liveboxandy/ZX-Max-128-Issue-3A/Step/DIP-16_W7.62mm_Socket.step

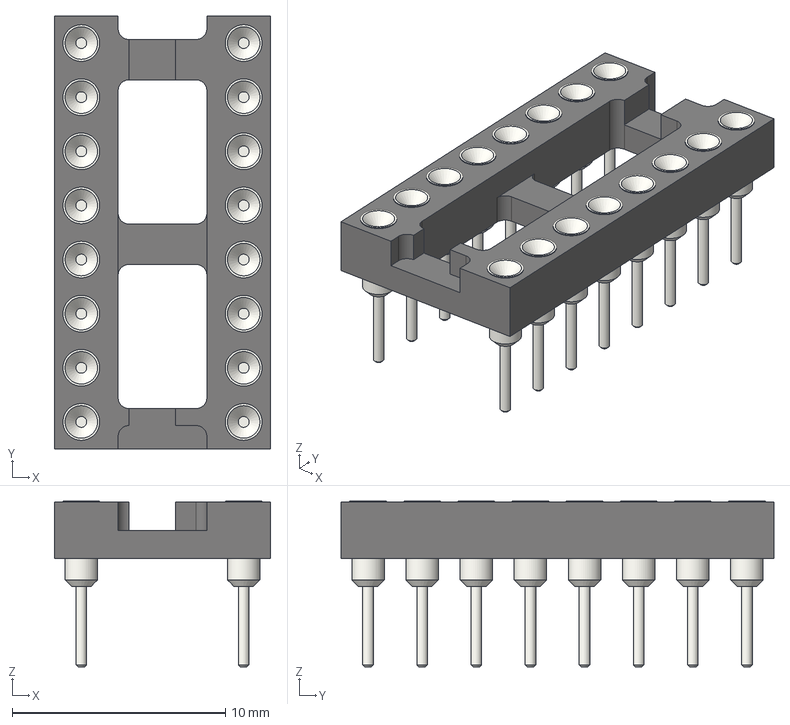
[picture p17: CAD file, 2026-07-10]
Step/DIP-16_W7.62mm_Socket.step
10.2 x 20.3 x 7.79 mm
