liveboxandy/ZX-Max-128-Issue-3A/Step/DIP-40_W15.24mm_Socket.step

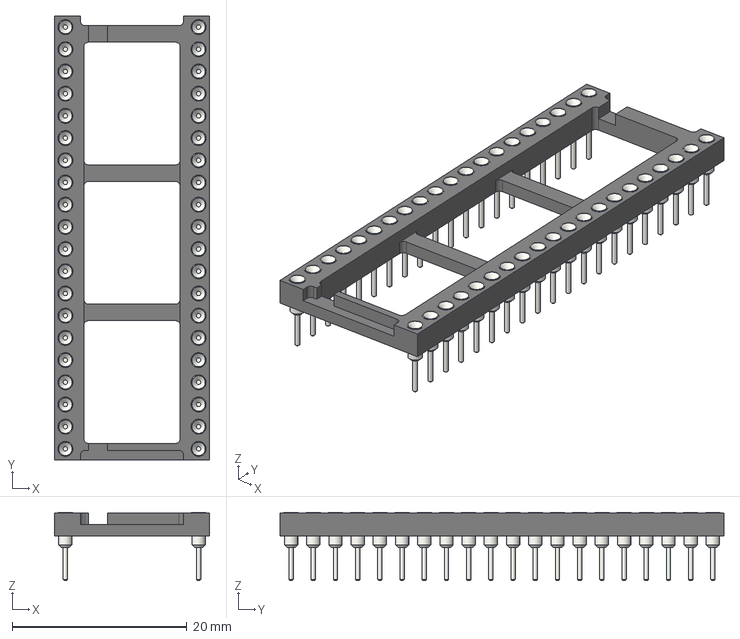
[picture p20: CAD file, 2026-07-10]
Step/DIP-40_W15.24mm_Socket.step
17.8 x 50.8 x 7.79 mm
