liveboxandy/ZX-Max-128-Issue-3A/Step/Voltage Regulator AZ1117IH-3.3TRG1.step

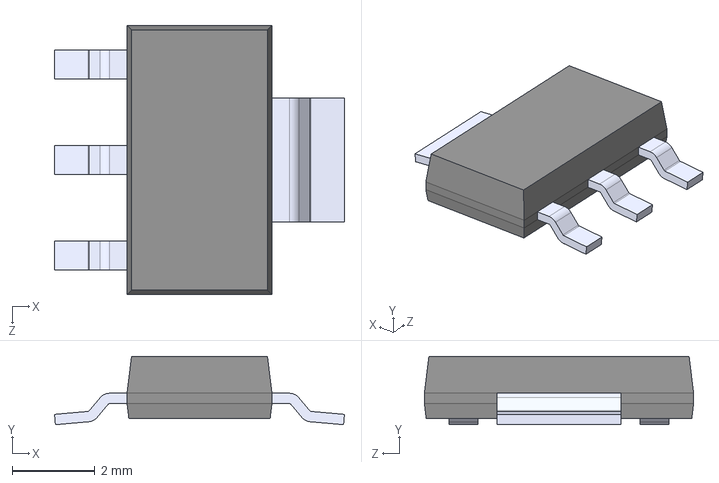
[picture p22: CAD file, 2026-07-10]
Step/Voltage Regulator AZ1117IH-3.3TRG1.step
7.00 x 1.65 x 6.50 mm
