liveboxandy/ZX-Max-128-Issue-3A/Step/PJ-002A.step

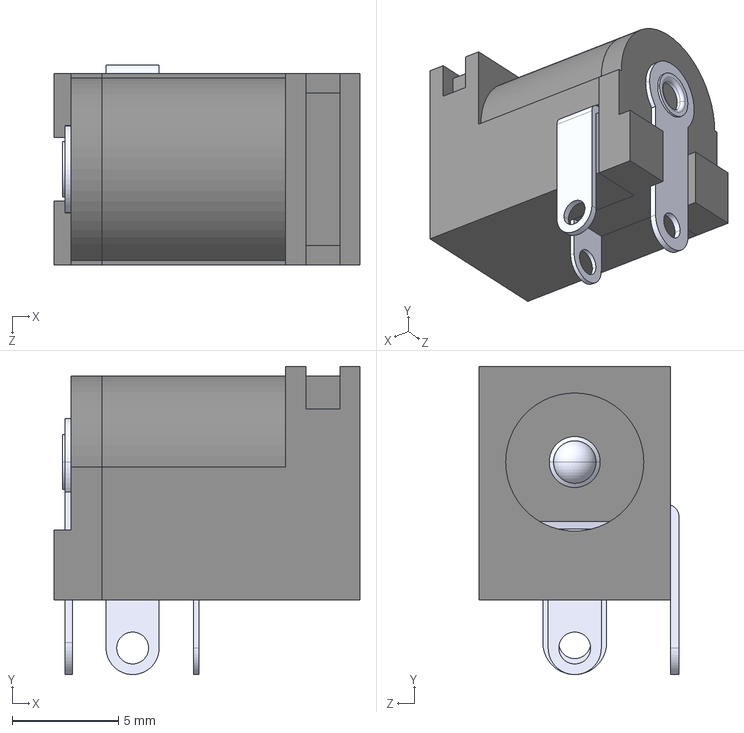
[picture p23: CAD file, 2026-07-10]
Step/PJ-002A.step
14.4 x 14.5 x 9.40 mm
