liveboxandy/ZX-Max-128-Issue-3A/Step/PLCC-84-AT.stp

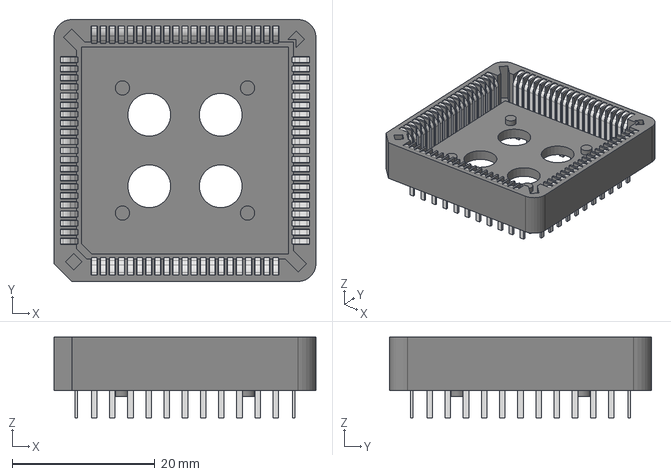
[picture p25: CAD file, 2026-07-10]
Step/PLCC-84-AT.stp
36.7 x 36.7 x 11.3 mm
