liveboxandy/ZX-Max-128-Issue-3A/Step/Capacitor 10nF 100V MLCC FA18C0G2A103JRU06.step

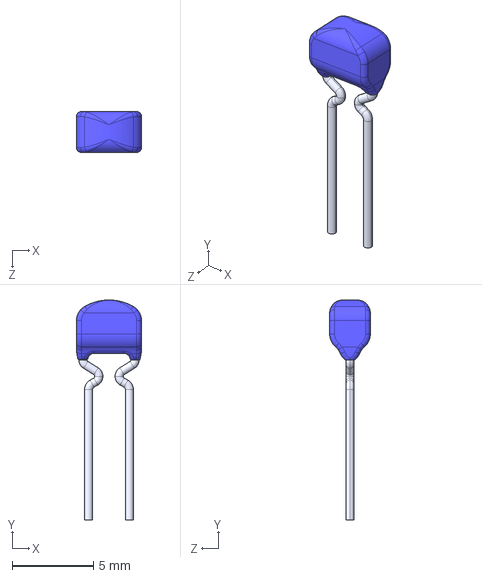
[picture p26: CAD file, 2026-07-10]
Step/Capacitor 10nF 100V MLCC FA18C0G2A103JRU06.step
4.00 x 13.5 x 2.50 mm
