liveboxandy/ZX-Max-128-Issue-3A/Step/DIP-16_W7.62mm.step

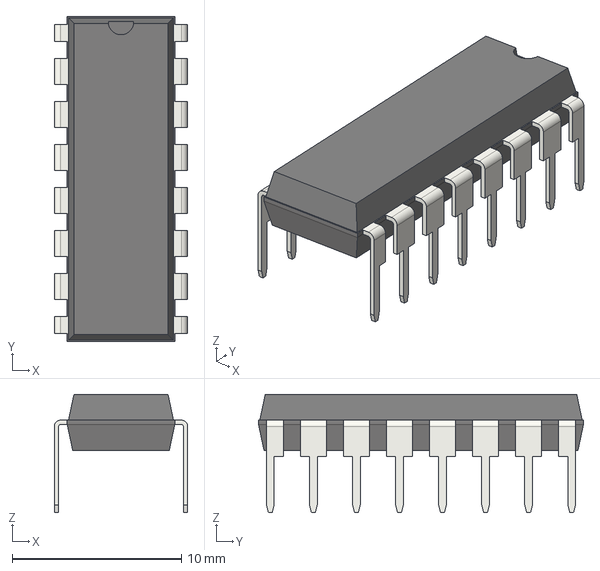
[picture p28: CAD file, 2026-07-10]
Step/DIP-16_W7.62mm.step
7.87 x 19.2 x 6.98 mm
