liveboxandy/ZX-Max-128-Issue-3A/Step/DIP-28_W15.24mm.step

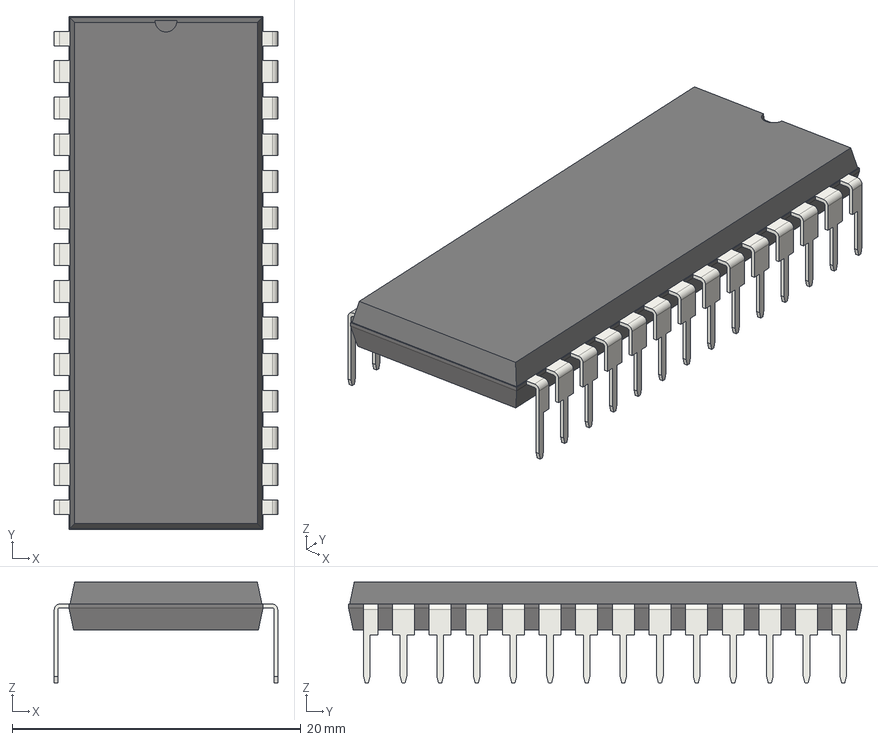
[picture p29: CAD file, 2026-07-10]
Step/DIP-28_W15.24mm.step
15.5 x 35.6 x 6.98 mm
