liveboxandy/ZX-Max-128-Issue-3A/Step/DIP-14_W7.62mm.step

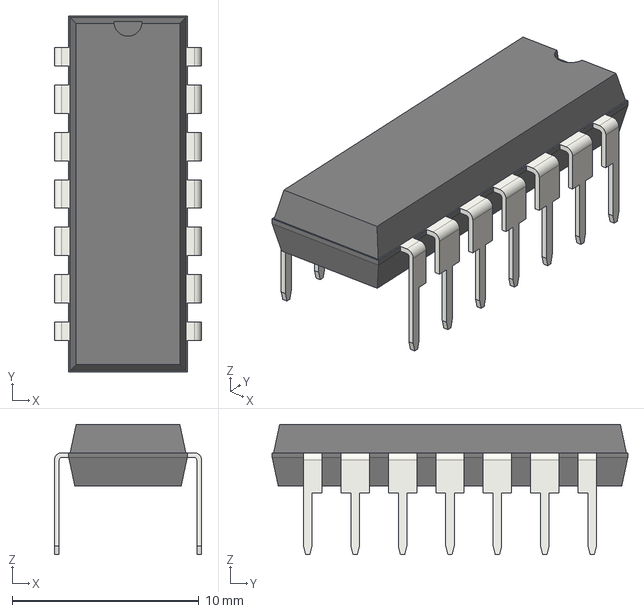
[picture p30: CAD file, 2026-07-10]
Step/DIP-14_W7.62mm.step
7.87 x 19.1 x 6.98 mm
