liveboxandy/ZX-Max-128-Issue-3A/Step/9Pin MiniDIN KMDGX-9S-BS-1_A1.IGS

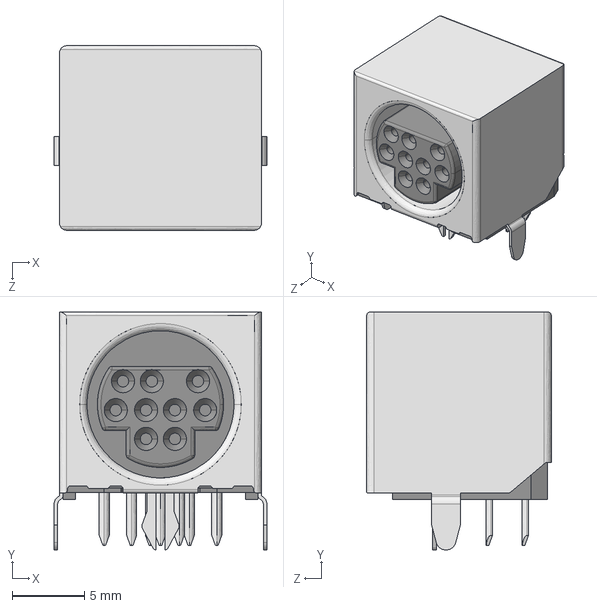
[picture p33: CAD file, 2026-07-10]
Step/9Pin MiniDIN KMDGX-9S-BS-1_A1.IGS
14.8 x 16.5 x 12.8 mm
