liveboxandy/ZX-Max-128-Issue-3A/Step/DIP-32_W15.24mm.step

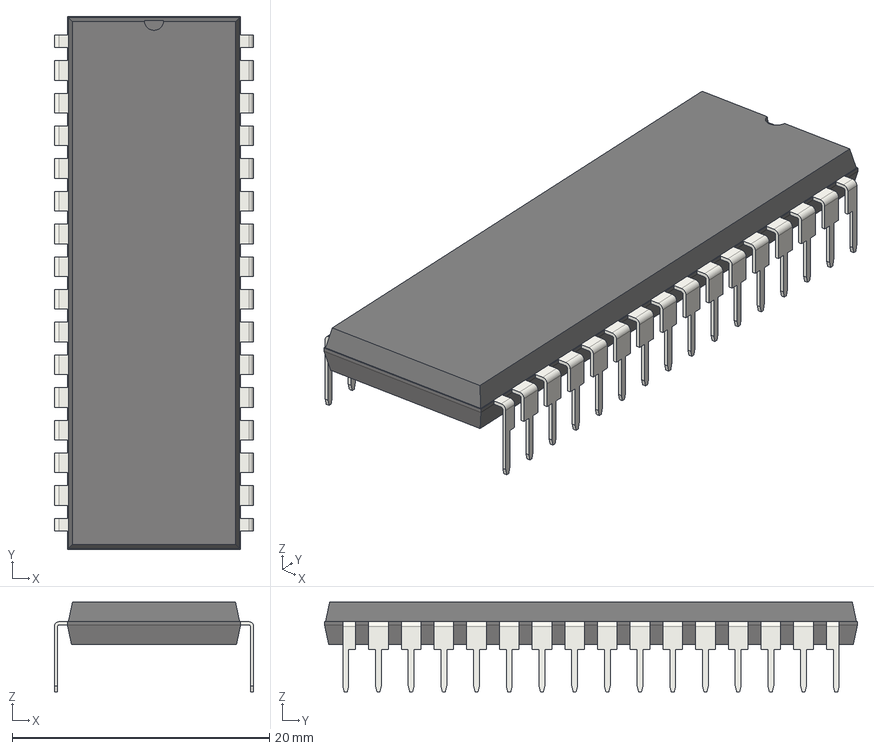
[picture p34: CAD file, 2026-07-10]
Step/DIP-32_W15.24mm.step
15.5 x 41.4 x 6.98 mm
