liveboxandy/ZX-Max-128-Issue-3A/Step/Capacitor 10uF 25V ECA-1EM100B.stp

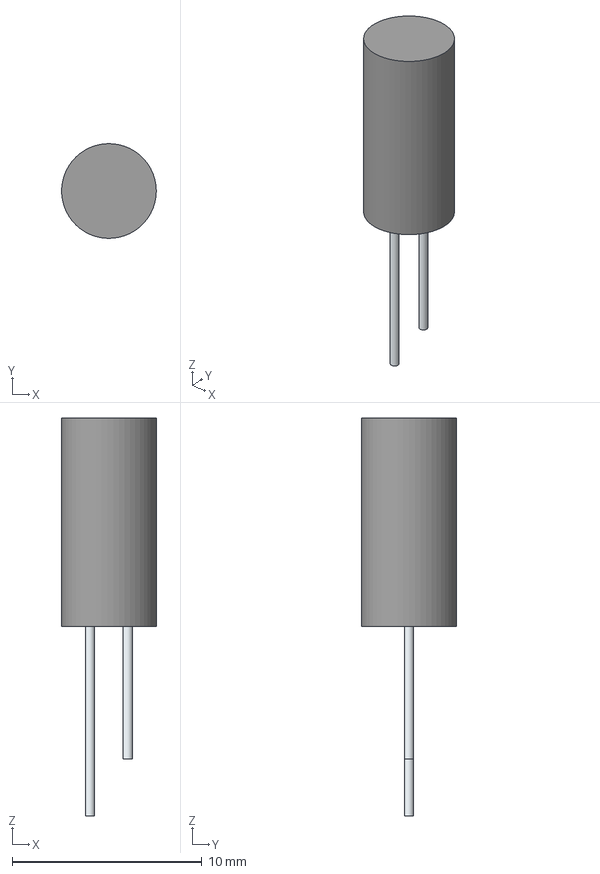
[picture p35: CAD file, 2026-07-10]
Step/Capacitor 10uF 25V ECA-1EM100B.stp
5.00 x 5.00 x 21.0 mm
SimpleBody
Pin1
Pin2
