liveboxandy/ZX-Max-128-Issue-3A/Step/Connector Pin-Pin 1x2 M20-9990246.step

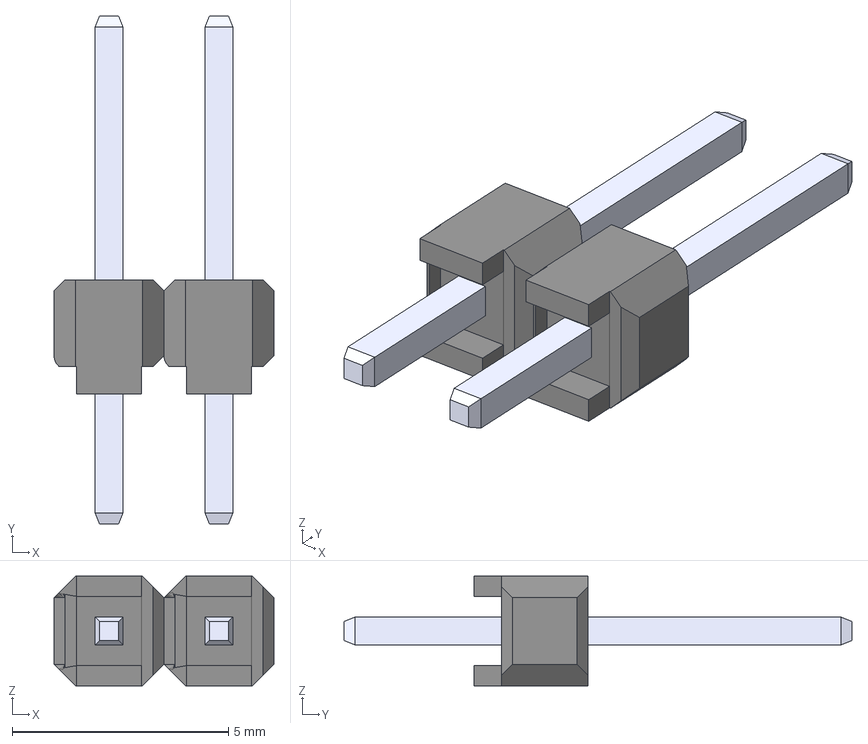
[picture p36: CAD file, 2026-07-10]
Step/Connector Pin-Pin 1x2 M20-9990246.step
5.08 x 11.7 x 2.54 mm
