liveboxandy/ZX-Max-128-Issue-3A/Step/9Pin MiniDIN KMDGX-9S-BS-1.stp

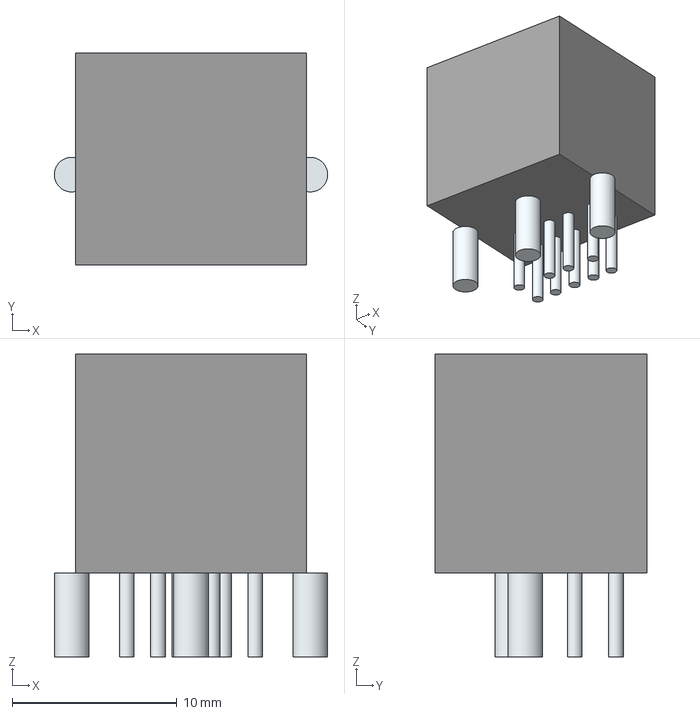
[picture p37: CAD file, 2026-07-10]
Step/9Pin MiniDIN KMDGX-9S-BS-1.stp
16.6 x 12.9 x 18.4 mm
Leads
