liveboxandy/ZX-Max-128-Issue-3A/Step/AS6C6264-55PCN.stp

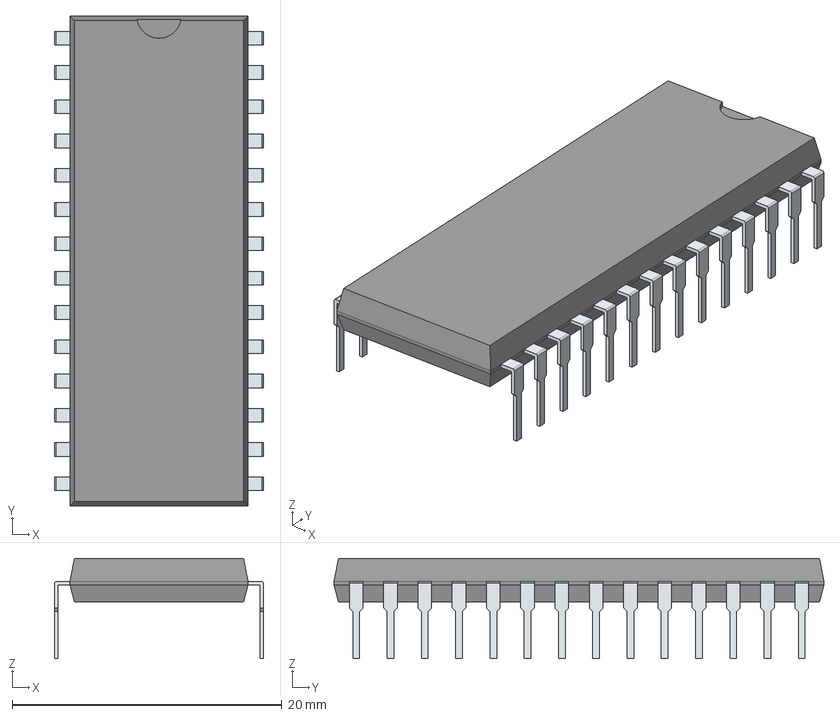
[picture p38: CAD file, 2026-07-10]
Step/AS6C6264-55PCN.stp
15.5 x 36.3 x 7.44 mm
PinsArrayLR
