liveboxandy/ZX-Max-128-Issue-3A/Step/AT27C256R-45PU.stp

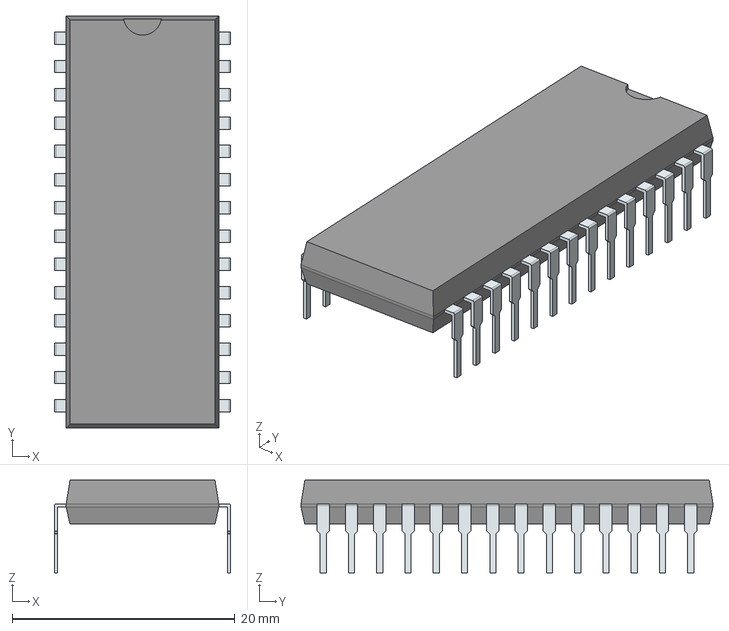
[picture p41: CAD file, 2026-07-10]
Step/AT27C256R-45PU.stp
15.8 x 37.0 x 8.33 mm
PinsArrayLR
