liveboxandy/ZX-Max-128-Issue-3A/CPU-ROM-RAM.kicad_sch

## KiCad design CPU-ROM-RAM.kicad_sch (2026-07-10)

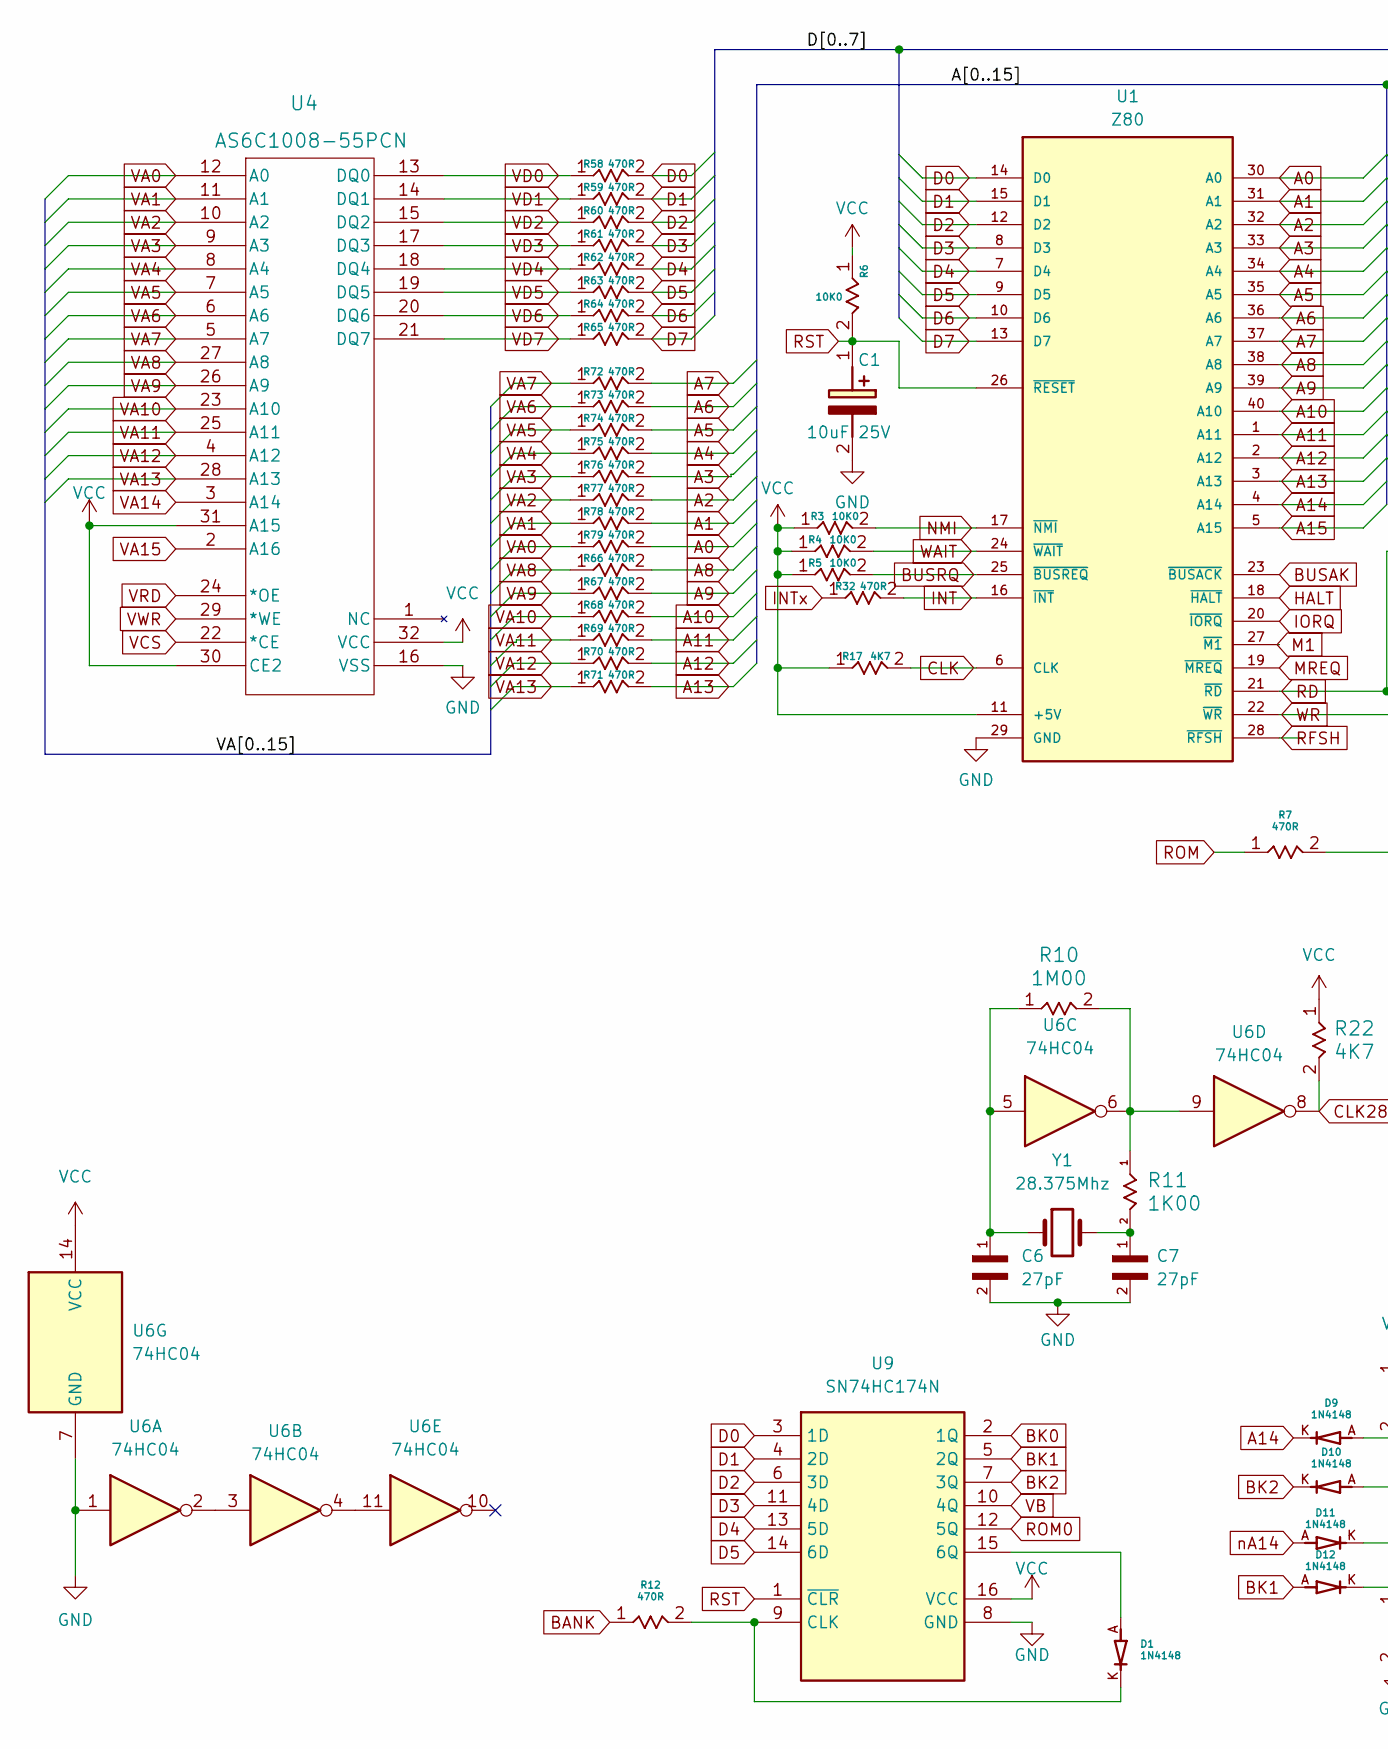
[picture p48: schematic CPU-ROM-RAM.kicad_sch, part in row 1, column 1]

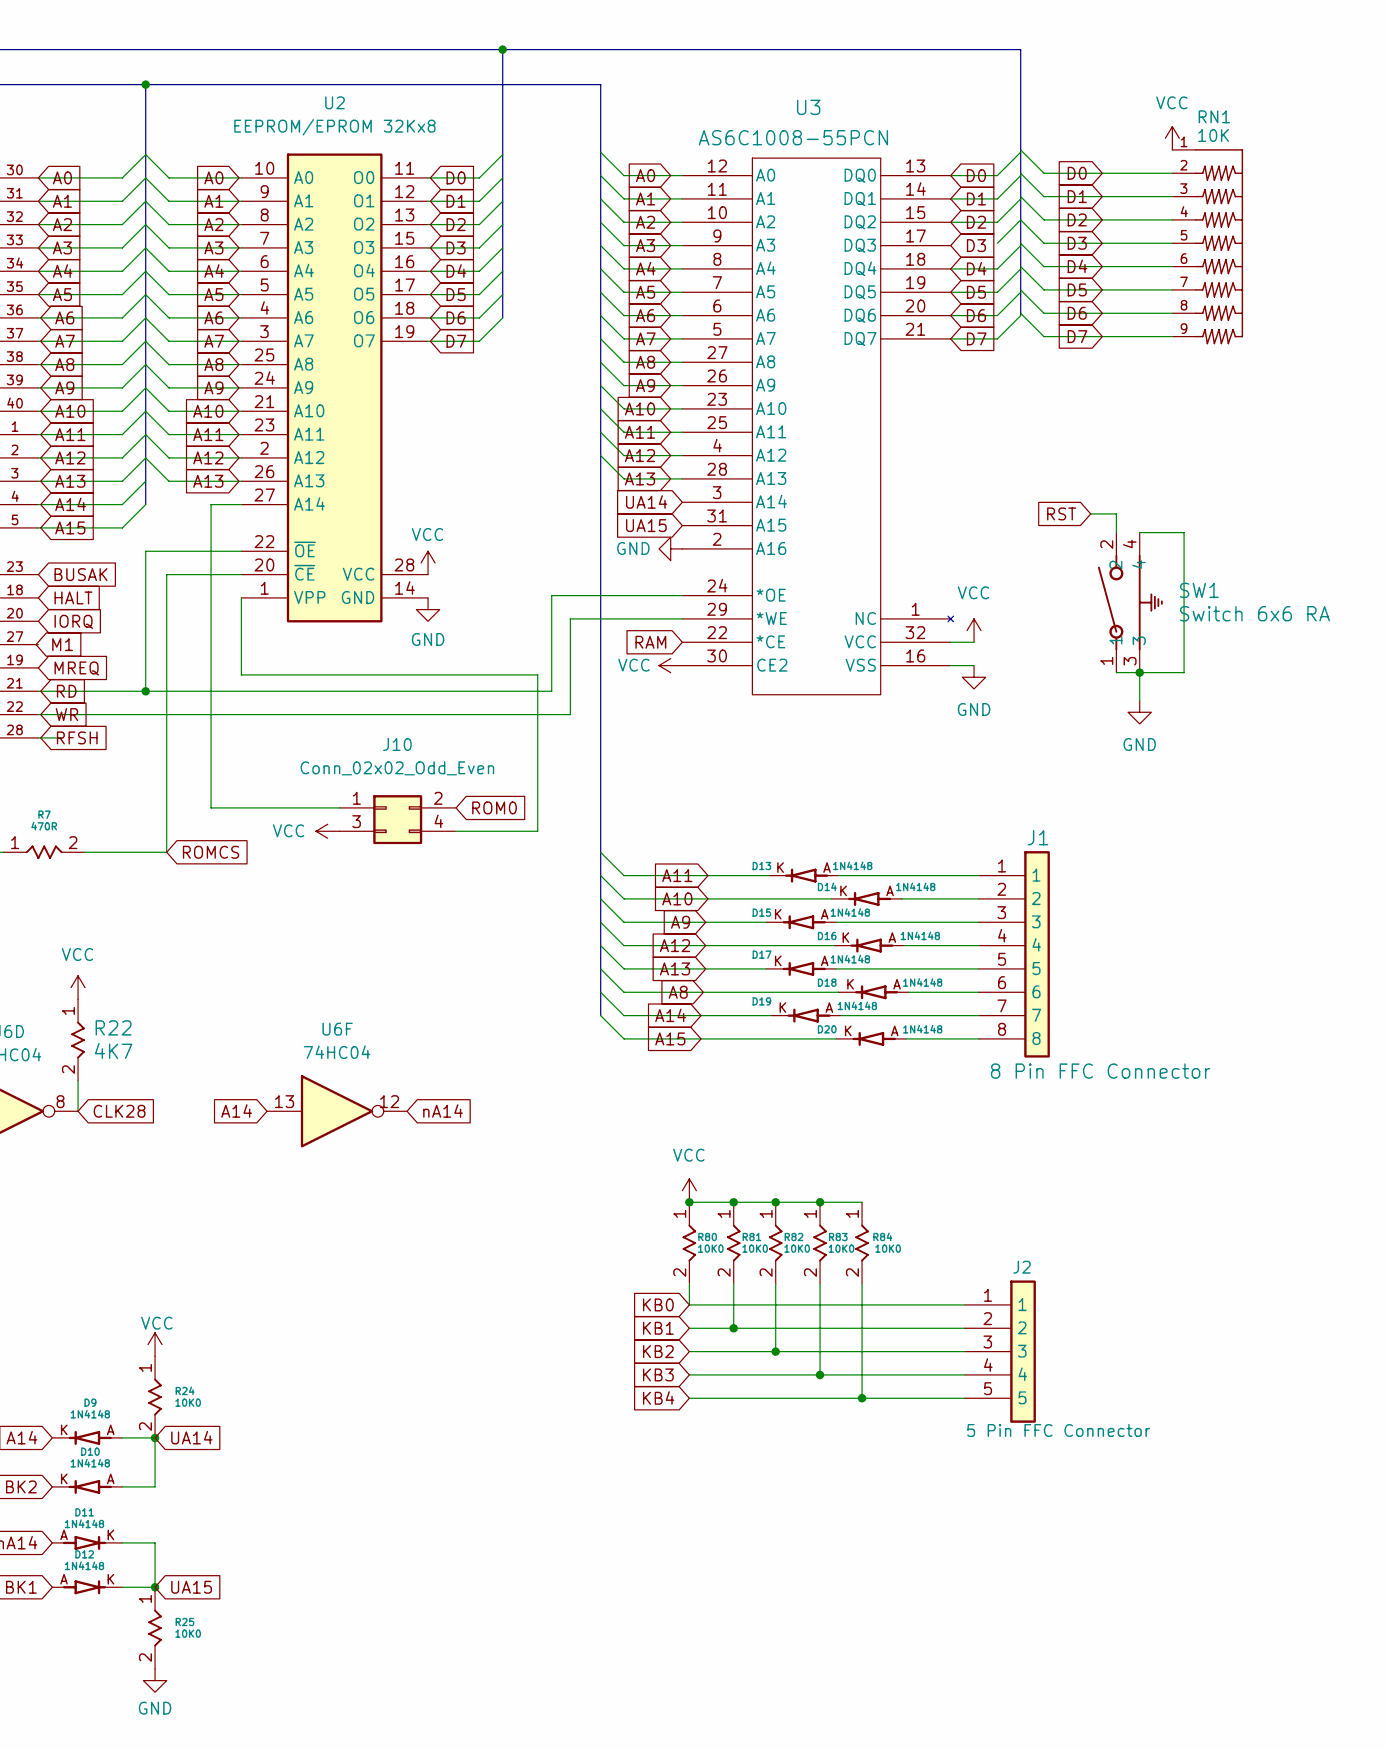
[picture p49: schematic CPU-ROM-RAM.kicad_sch, part in row 1, column 2]

Parts:
C1: 10uF 25V; CAPPRD200W50D500H1100; Mouser Part Number 667-ECA-1EM100B
C6, C7: 27pF; CAPRB250W50L400T250H550; PARTREV 20200310
D1, D9, D10, D11, D12, D13, D14, D15, D16, D17, D18, D19, D20: 1N4148; DIOAD753W49L380D172B; PARTREV 5
J1: 8 Pin FFC Connector; 55203155
J2: 5 Pin FFC Connector; 55203155; Mouser Part Number 571-5-520315-5
J10: Conn_02x02_Odd_Even; PinHeader_2x02_P2.54mm_Vertical
R3, R4, R5, R6, R24, R25, R80, R81, R82, R83, R84: 10K0; STA_CF14_STP
R7, R12, R32, R58, R59, R60, R61, R62, R63, R64, R65, R66, R67, R68, R69, R70, R71, R72, R73, R74, R75, R76, R77, R78, R79: 470R; STA_CF14_STP
R10: 1M00; STA_CF14_STP
R11: 1K00; STA_CF14_STP
R17, R22: 4K7; STA_CF14_STP
RN1: 10K; SIP249W50P254L2281H508Q9; PARTREV 10/1/20
SW1: Switch 6x6 RA; SW2_1825027-G_TEC
U1: Z80; Z80_Socket
U2: EEPROM/EPROM 32Kx8; DIP1556W56P254L3702H483Q28N; Mouser Part Number 556-AT27C256R-45PU
U3: AS6C1008-55PCN; U3
U4: AS6C1008-55PCN; PDIP-32_MIL600_ALL
U6: 74HC04; DIP794W53P254L1930H508Q14N
U9: SN74HC174N; DIP794W53P254L1930H508Q16N; Mouser Part Number 595-SN74HC174N
Y1: 28.375Mhz; Crystal_HC49-4H_Vertical

Connections:
A0: R79.2, U1.30 (A0), U2.10 (A0), U3.12 (A0)
A1: R78.2, U1.31 (A1), U2.9 (A1), U3.11 (A1)
A2: R77.2, U1.32 (A2), U2.8 (A2), U3.10 (A2)
A3: R76.2, U1.33 (A3), U2.7 (A3), U3.9 (A3)
A4: R75.2, U1.34 (A4), U2.6 (A4), U3.8 (A4)
A5: R74.2, U1.35 (A5), U2.5 (A5), U3.7 (A5)
A6: R73.2, U1.36 (A6), U2.4 (A6), U3.6 (A6)
A7: R72.2, U1.37 (A7), U2.3 (A7), U3.5 (A7)
A8: D18.K, R66.2, U1.38 (A8), U2.25 (A8), U3.27 (A8)
A9: D15.K, R67.2, U1.39 (A9), U2.24 (A9), U3.26 (A9)
A10: D14.K, R68.2, U1.40 (A10), U2.21 (A10), U3.23 (A10)
A11: D13.K, R69.2, U1.1 (A11), U2.23 (A11), U3.25 (A11)
A12: D16.K, R70.2, U1.2 (A12), U2.2 (A12), U3.4 (A12)
A13: D17.K, R71.2, U1.3 (A13), U2.26 (A13), U3.28 (A13)
A14: D9.K, D19.K, U1.4 (A14), U6.13
A15: D20.K, U1.5 (A15)
BANK: R12.1
BK0: U9.2 (1Q)
BK1: D12.A, U9.5 (2Q)
BK2: D10.K, U9.7 (3Q)
BUSAK: U1.23 (~BUSACK)
BUSRQ: R5.2, U1.25 (~BUSREQ)
CLK: R17.2, U1.6 (CLK)
CLK28: R22.2, U6.8
D0: R58.2, RN1.2, U1.14 (D0), U2.11 (O0), U3.13 (DQ0), U9.3 (1D)
D1: R59.2, RN1.3, U1.15 (D1), U2.12 (O1), U3.14 (DQ1), U9.4 (2D)
D2: R60.2, RN1.4, U1.12 (D2), U2.13 (O2), U3.15 (DQ2), U9.6 (3D)
D3: R61.2, RN1.5, U1.8 (D3), U2.15 (O3), U3.17 (DQ3), U9.11 (4D)
D4: R62.2, RN1.6, U1.7 (D4), U2.16 (O4), U3.18 (DQ4), U9.13 (5D)
D5: R63.2, RN1.7, U1.9 (D5), U2.17 (O5), U3.19 (DQ5), U9.14 (6D)
D6: R64.2, RN1.8, U1.10 (D6), U2.18 (O6), U3.20 (DQ6)
D7: R65.2, RN1.9, U1.13 (D7), U2.19 (O7), U3.21 (DQ7)
GND: C1.2 (-), C6.2, C7.2, R25.2, SW1.1, SW1.3, SW1.4, U1.29 (GND), U2.14 (GND), U3.2 (A16), U3.16 (VSS), U4.16 (VSS), U6.1, U6.7 (GND), U9.8 (GND)
HALT: U1.18 (~HALT)
INT: R32.2, U1.16 (~INT)
INTx: R32.1
IORQ: U1.20 (~IORQ)
KB0: J2.1, R80.2
KB1: J2.2, R81.2
KB2: J2.3, R82.2
KB3: J2.4, R83.2
KB4: J2.5, R84.2
M1: U1.27 (~M1)
MREQ: U1.19 (~MREQ)
NMI: R3.2, U1.17 (~NMI)
unnamed: C6.1, R10.1, U6.5, Y1.1
unnamed: C7.1, R11.2, Y1.2
unnamed: D1.A, U9.15 (6Q)
unnamed: D1.K, R12.2, U9.9 (CLK)
unnamed: D13.A, J1.1
unnamed: D14.A, J1.2
unnamed: D15.A, J1.3
unnamed: D16.A, J1.4
unnamed: D17.A, J1.5
unnamed: D18.A, J1.6
unnamed: D19.A, J1.7
unnamed: D20.A, J1.8
unnamed: J10.1, U2.27 (A14)
unnamed: J10.4, U2.1 (VPP)
unnamed: R10.2, R11.1, U6.6, U6.9
unnamed: U6.2, U6.3
unnamed: U6.4, U6.11
RAM: U3.22 (*CE)
RD: U1.21 (~RD), U2.22 (~OE), U3.24 (*OE)
RFSH: U1.28 (~RFSH)
ROM: R7.1
ROM0: J10.2, U9.12 (5Q)
ROMCS: R7.2, U2.20 (~CE)
RST: C1.1 (+), R6.2, SW1.2, U1.26 (~RESET), U9.1 (~CLR)
UA14: D9.A, D10.A, R24.2, U3.3 (A14)
UA15: D11.K, D12.K, R25.1, U3.31 (A15)
VA0: R79.1, U4.12 (A0)
VA1: R78.1, U4.11 (A1)
VA2: R77.1, U4.10 (A2)
VA3: R76.1, U4.9 (A3)
VA4: R75.1, U4.8 (A4)
VA5: R74.1, U4.7 (A5)
VA6: R73.1, U4.6 (A6)
VA7: R72.1, U4.5 (A7)
VA8: R66.1, U4.27 (A8)
VA9: R67.1, U4.26 (A9)
VA10: R68.1, U4.23 (A10)
VA11: R69.1, U4.25 (A11)
VA12: R70.1, U4.4 (A12)
VA13: R71.1, U4.28 (A13)
VA14: U4.3 (A14)
VA15: U4.2 (A16)
VB: U9.10 (4Q)
VCC: J10.3, R3.1, R4.1, R5.1, R6.1, R17.1, R22.1, R24.1, R80.1, R81.1, R82.1, R83.1, R84.1, RN1.1, U1.11 (+5V), U2.28 (VCC), U3.30 (CE2), U3.32 (VCC), U4.30 (CE2), U4.31 (A15), U4.32 (VCC), U6.14 (VCC), U9.16 (VCC)
VCS: U4.22 (*CE)
VD0: R58.1, U4.13 (DQ0)
VD1: R59.1, U4.14 (DQ1)
VD2: R60.1, U4.15 (DQ2)
VD3: R61.1, U4.17 (DQ3)
VD4: R62.1, U4.18 (DQ4)
VD5: R63.1, U4.19 (DQ5)
VD6: R64.1, U4.20 (DQ6)
VD7: R65.1, U4.21 (DQ7)
VRD: U4.24 (*OE)
VWR: U4.29 (*WE)
WAIT: R4.2, U1.24 (~WAIT)
WR: U1.22 (~WR), U3.29 (*WE)
nA14: D11.A, U6.12
