liveboxandy/ZX-Max-128-Issue-3A/EPM7128S.kicad_sch

## KiCad design EPM7128S.kicad_sch (2026-07-10)

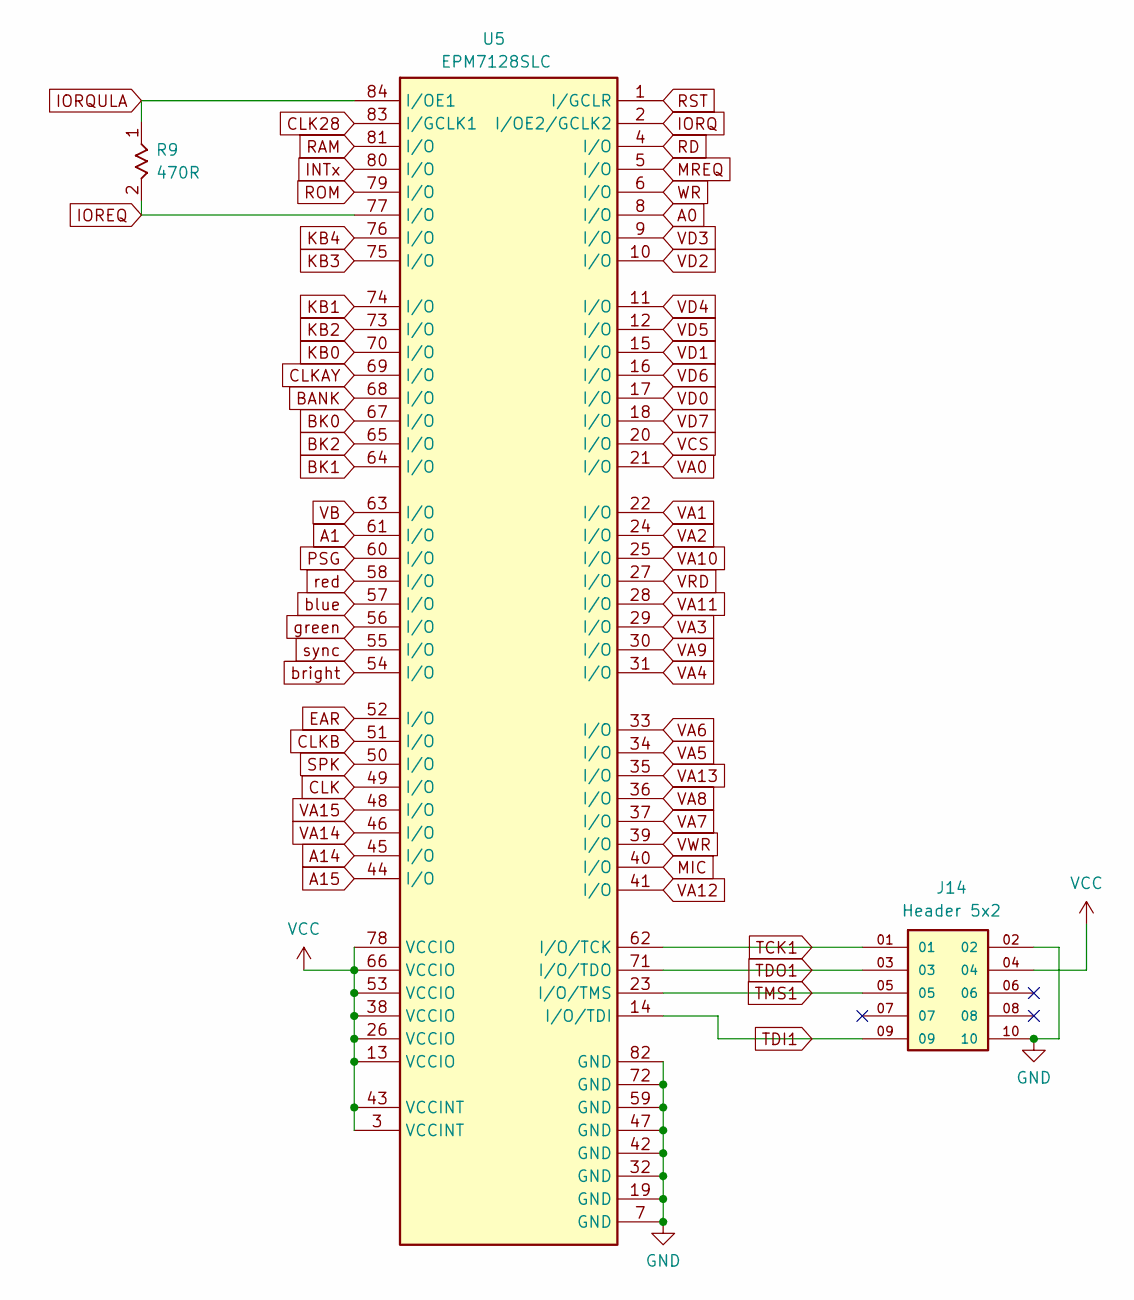
[picture p50: schematic EPM7128S.kicad_sch]

Parts:
J14: Header 5x2; AMPHENOL_10129381-910002BLF; PARTREV D
R9: 470R; STA_CF14_STP
U5: EPM7128SLC; PLCC84AT

Connections:
A0: U5.8 (I/O)
A1: U5.61 (I/O)
A14: U5.45 (I/O)
A15: U5.44 (I/O)
BANK: U5.68 (I/O)
BK0: U5.67 (I/O)
BK1: U5.64 (I/O)
BK2: U5.65 (I/O)
CLK: U5.49 (I/O)
CLK28: U5.83 (I/GCLK1)
CLKAY: U5.69 (I/O)
CLKB: U5.51 (I/O)
EAR: U5.52 (I/O)
GND: J14.02, J14.10, U5.7 (GND), U5.19 (GND), U5.32 (GND), U5.42 (GND), U5.47 (GND), U5.59 (GND), U5.72 (GND), U5.82 (GND)
INTx: U5.80 (I/O)
IOREQ: R9.2, U5.77 (I/O)
IORQ: U5.2 (I/OE2/GCLK2)
IORQULA: R9.1, U5.84 (I/OE1)
KB0: U5.70 (I/O)
KB1: U5.74 (I/O)
KB2: U5.73 (I/O)
KB3: U5.75 (I/O)
KB4: U5.76 (I/O)
MIC: U5.40 (I/O)
MREQ: U5.5 (I/O)
PSG: U5.60 (I/O)
RAM: U5.81 (I/O)
RD: U5.4 (I/O)
ROM: U5.79 (I/O)
RST: U5.1 (I/GCLR)
SPK: U5.50 (I/O)
TCK1: J14.01, U5.62 (I/O/TCK)
TDI1: J14.09, U5.14 (I/O/TDI)
TDO1: J14.03, U5.71 (I/O/TDO)
TMS1: J14.05, U5.23 (I/O/TMS)
VA0: U5.21 (I/O)
VA1: U5.22 (I/O)
VA2: U5.24 (I/O)
VA3: U5.29 (I/O)
VA4: U5.31 (I/O)
VA5: U5.34 (I/O)
VA6: U5.33 (I/O)
VA7: U5.37 (I/O)
VA8: U5.36 (I/O)
VA9: U5.30 (I/O)
VA10: U5.25 (I/O)
VA11: U5.28 (I/O)
VA12: U5.41 (I/O)
VA13: U5.35 (I/O)
VA14: U5.46 (I/O)
VA15: U5.48 (I/O)
VB: U5.63 (I/O)
VCC: J14.04, U5.3 (VCCINT), U5.13 (VCCIO), U5.26 (VCCIO), U5.38 (VCCIO), U5.43 (VCCINT), U5.53 (VCCIO), U5.66 (VCCIO), U5.78 (VCCIO)
VCS: U5.20 (I/O)
VD0: U5.17 (I/O)
VD1: U5.15 (I/O)
VD2: U5.10 (I/O)
VD3: U5.9 (I/O)
VD4: U5.11 (I/O)
VD5: U5.12 (I/O)
VD6: U5.16 (I/O)
VD7: U5.18 (I/O)
VRD: U5.27 (I/O)
VWR: U5.39 (I/O)
WR: U5.6 (I/O)
blue: U5.57 (I/O)
bright: U5.54 (I/O)
green: U5.56 (I/O)
red: U5.58 (I/O)
sync: U5.55 (I/O)
