liveboxandy/ZX-Max-128-Issue-3A/Power&Filter.kicad_sch

## KiCad design Power&Filter.kicad_sch (2026-07-10)

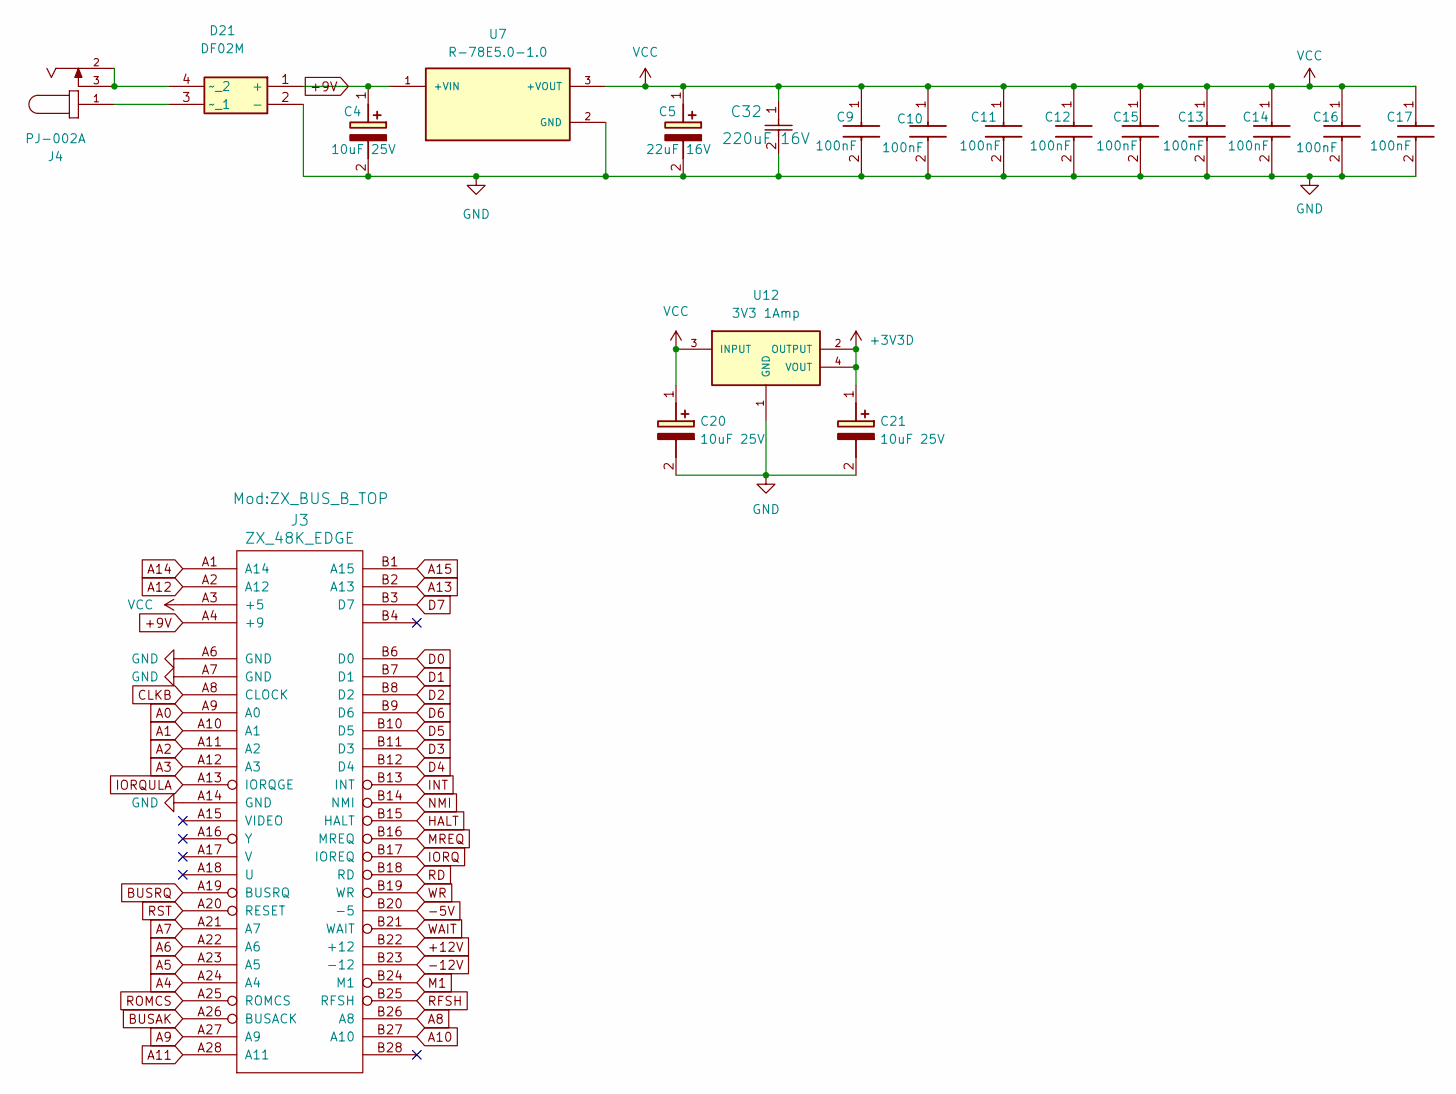
[picture p51: schematic Power&Filter.kicad_sch]

Parts:
C4, C20, C21: 10uF 25V; CAPPRD200W50D500H1100; Mouser Part Number 667-ECA-1EM100B
C5: 22uF 16V; CAPPRD200W50D500H1100; Mouser Part Number 667-ECA-1EM100B
C9, C10, C11, C12, C13, C14, C16, C17: 100nF; CAPRB250W50L400T250H550; Mouser Part Number 594-K104Z15Y5VF5TL2
C15: 100nF; Capacitor 3.8mm PItch; Mouser Part Number 594-K104Z15Y5VF5TL2
C32: 220uF 16V; CAP_YX_6P3X11_RUB
D21: DF02M; DIP825W58P510L832H543Q4N; Mouser Part Number 621-DF02M
J3: ZX_48K_EDGE; ZX_BUS_B_TOP
J4: PJ-002A; CUI_PJ-002A
U7: R-78E5.0-1.0; CONV_R-78E5.0-1.0; PARTREV 6
U12: 3V3 1Amp; SOT230P700X185-4N

Connections:
+3V3D: C21.1 (+), U12.2 (OUTPUT), U12.4 (VOUT)
+9V: C4.1 (+), D21.1 (+), J3.A4 (+9), U7.1 (+VIN)
+12V: J3.B22 (+12)
-5V: J3.B20 (-5)
-12V: J3.B23 (-12)
A0: J3.A9 (A0)
A1: J3.A10 (A1)
A2: J3.A11 (A2)
A3: J3.A12 (A3)
A4: J3.A24 (A4)
A5: J3.A23 (A5)
A6: J3.A22 (A6)
A7: J3.A21 (A7)
A8: J3.B26 (A8)
A9: J3.A27 (A9)
A10: J3.B27 (A10)
A11: J3.A28 (A11)
A12: J3.A2 (A12)
A13: J3.B2 (A13)
A14: J3.A1 (A14)
A15: J3.B1 (A15)
BUSAK: J3.A26 (BUSACK)
BUSRQ: J3.A19 (BUSRQ)
CLKB: J3.A8 (CLOCK)
D0: J3.B6 (D0)
D1: J3.B7 (D1)
D2: J3.B8 (D2)
D3: J3.B11 (D3)
D4: J3.B12 (D4)
D5: J3.B10 (D5)
D6: J3.B9 (D6)
D7: J3.B3 (D7)
GND: C4.2 (-), C5.2 (-), C9.2 (-), C10.2 (-), C11.2 (-), C12.2 (-), C13.2 (-), C14.2 (-), C15.2 (-), C16.2 (-), C17.2 (-), C20.2 (-), C21.2 (-), C32.2, D21.2 (-), J3.A6 (GND), J3.A7 (GND), J3.A14 (GND), U7.2 (GND), U12.1 (GND)
HALT: J3.B15 (HALT)
INT: J3.B13 (INT)
IORQ: J3.B17 (IOREQ)
IORQULA: J3.A13 (IORQGE)
M1: J3.B24 (M1)
MREQ: J3.B16 (MREQ)
NMI: J3.B14 (NMI)
unnamed: D21.3 (~_1), J4.1
unnamed: D21.4 (~_2), J4.2, J4.3
RD: J3.B18 (RD)
RFSH: J3.B25 (RFSH)
ROMCS: J3.A25 (ROMCS)
RST: J3.A20 (RESET)
VCC: C5.1 (+), C9.1 (+), C10.1 (+), C11.1 (+), C12.1 (+), C13.1 (+), C14.1 (+), C15.1 (+), C16.1 (+), C17.1 (+), C20.1 (+), C32.1, J3.A3 (+5), U7.3 (+VOUT), U12.3 (INPUT)
WAIT: J3.B21 (WAIT)
WR: J3.B19 (WR)
