liveboxandy/ZX-Max-128-Issue-3A/Turbo Sound.kicad_sch

## KiCad design Turbo Sound.kicad_sch (2026-07-10)

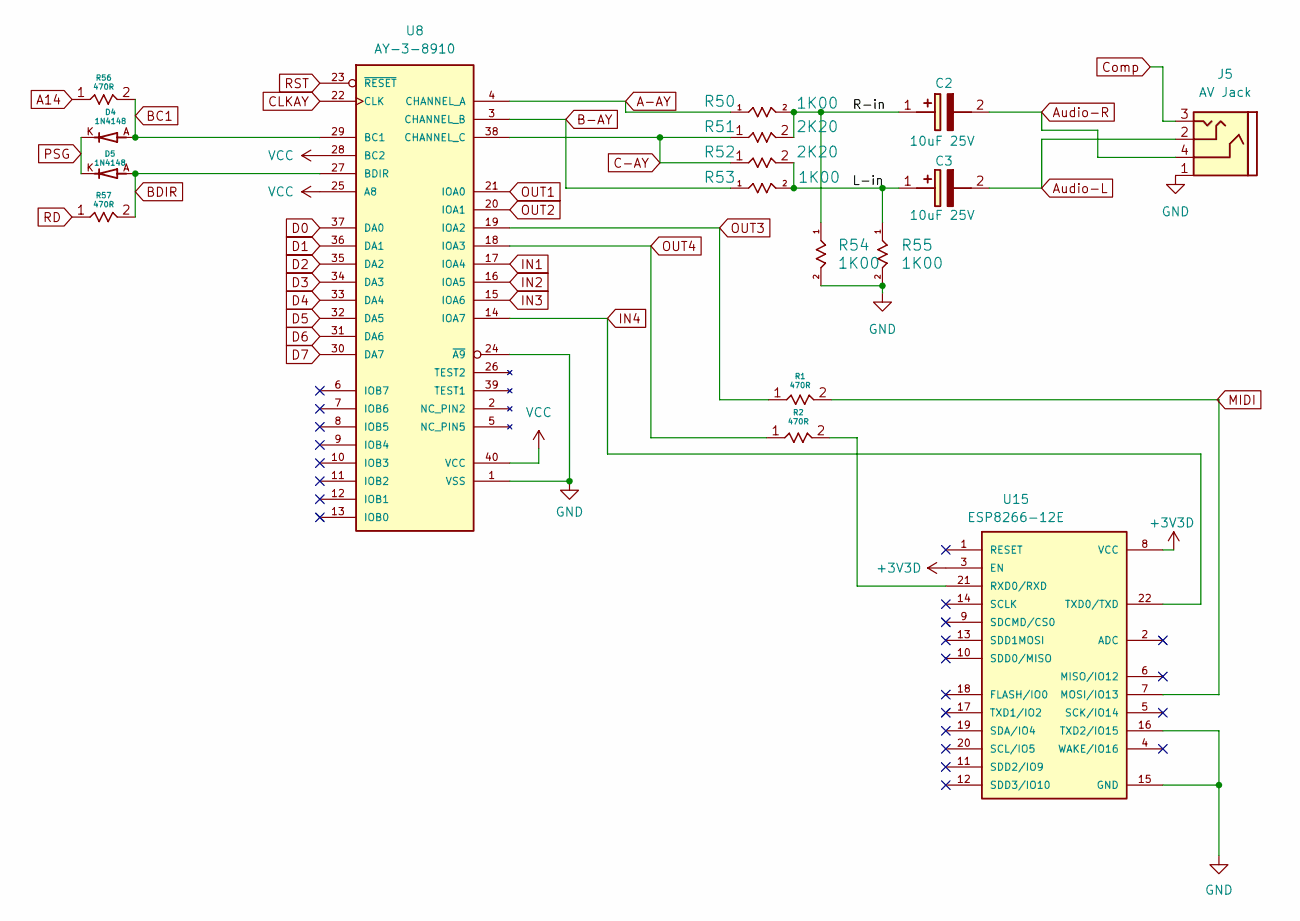
[picture p52: schematic Turbo Sound.kicad_sch]

Parts:
C2, C3: 10uF 25V; CAPPRD200W50D500H1100; Mouser Part Number 667-ECA-1EM100B
D4, D5: 1N4148; DIOAD753W49L380D172B; PARTREV 5
J5: AV Jack; PJ-322A
R1, R2, R56, R57: 470R; STA_CF14_STP
R50, R53, R54, R55: 1K00; STA_CF14_STP
R51, R52: 2K20; STA_CF14_STP
U8: AY-3-8910; Z80_Socket
U15: ESP8266-12E; WIFI_Module_ESP8266_12E

Connections:
+3V3D: U15.3 (EN), U15.8 (VCC)
A14: R56.1
A-AY: R50.1, U8.4 (CHANNEL_A)
Audio-L: C3.2 (-), J5.2
Audio-R: C2.2 (-), J5.4
B-AY: R53.1, U8.3 (CHANNEL_B)
BC1: D4.A, R56.2, U8.29 (BC1)
BDIR: D5.A, R57.2, U8.27 (BDIR)
C-AY: R51.1, R52.1, U8.38 (CHANNEL_C)
CLKAY: U8.22 (CLK)
Comp: J5.3
D0: U8.37 (DA0)
D1: U8.36 (DA1)
D2: U8.35 (DA2)
D3: U8.34 (DA3)
D4: U8.33 (DA4)
D5: U8.32 (DA5)
D6: U8.31 (DA6)
D7: U8.30 (DA7)
GND: J5.1, R54.2, R55.2, U8.1 (VSS), U8.24 (~A9), U15.15 (GND), U15.16 (TXD2/IO15)
IN1: U8.17 (IOA4)
IN2: U8.16 (IOA5)
IN3: U8.15 (IOA6)
IN4: U8.14 (IOA7), U15.22 (TXD0/TXD)
L-in: C3.1 (+), R52.2, R53.2, R55.1
MIDI: R1.2, U15.7 (MOSI/IO13)
unnamed: R2.2, U15.21 (RXD0/RXD)
OUT1: U8.21 (IOA0)
OUT2: U8.20 (IOA1)
OUT3: R1.1, U8.19 (IOA2)
OUT4: R2.1, U8.18 (IOA3)
PSG: D4.K, D5.K
R-in: C2.1 (+), R50.2, R51.2, R54.1
RD: R57.1
RST: U8.23 (~RESET)
VCC: U8.25 (A8), U8.28 (BC2), U8.40 (VCC)
