liveboxandy/ZX-Max-128-Issue-3A/Video.kicad_sch

## KiCad design Video.kicad_sch (2026-07-10)

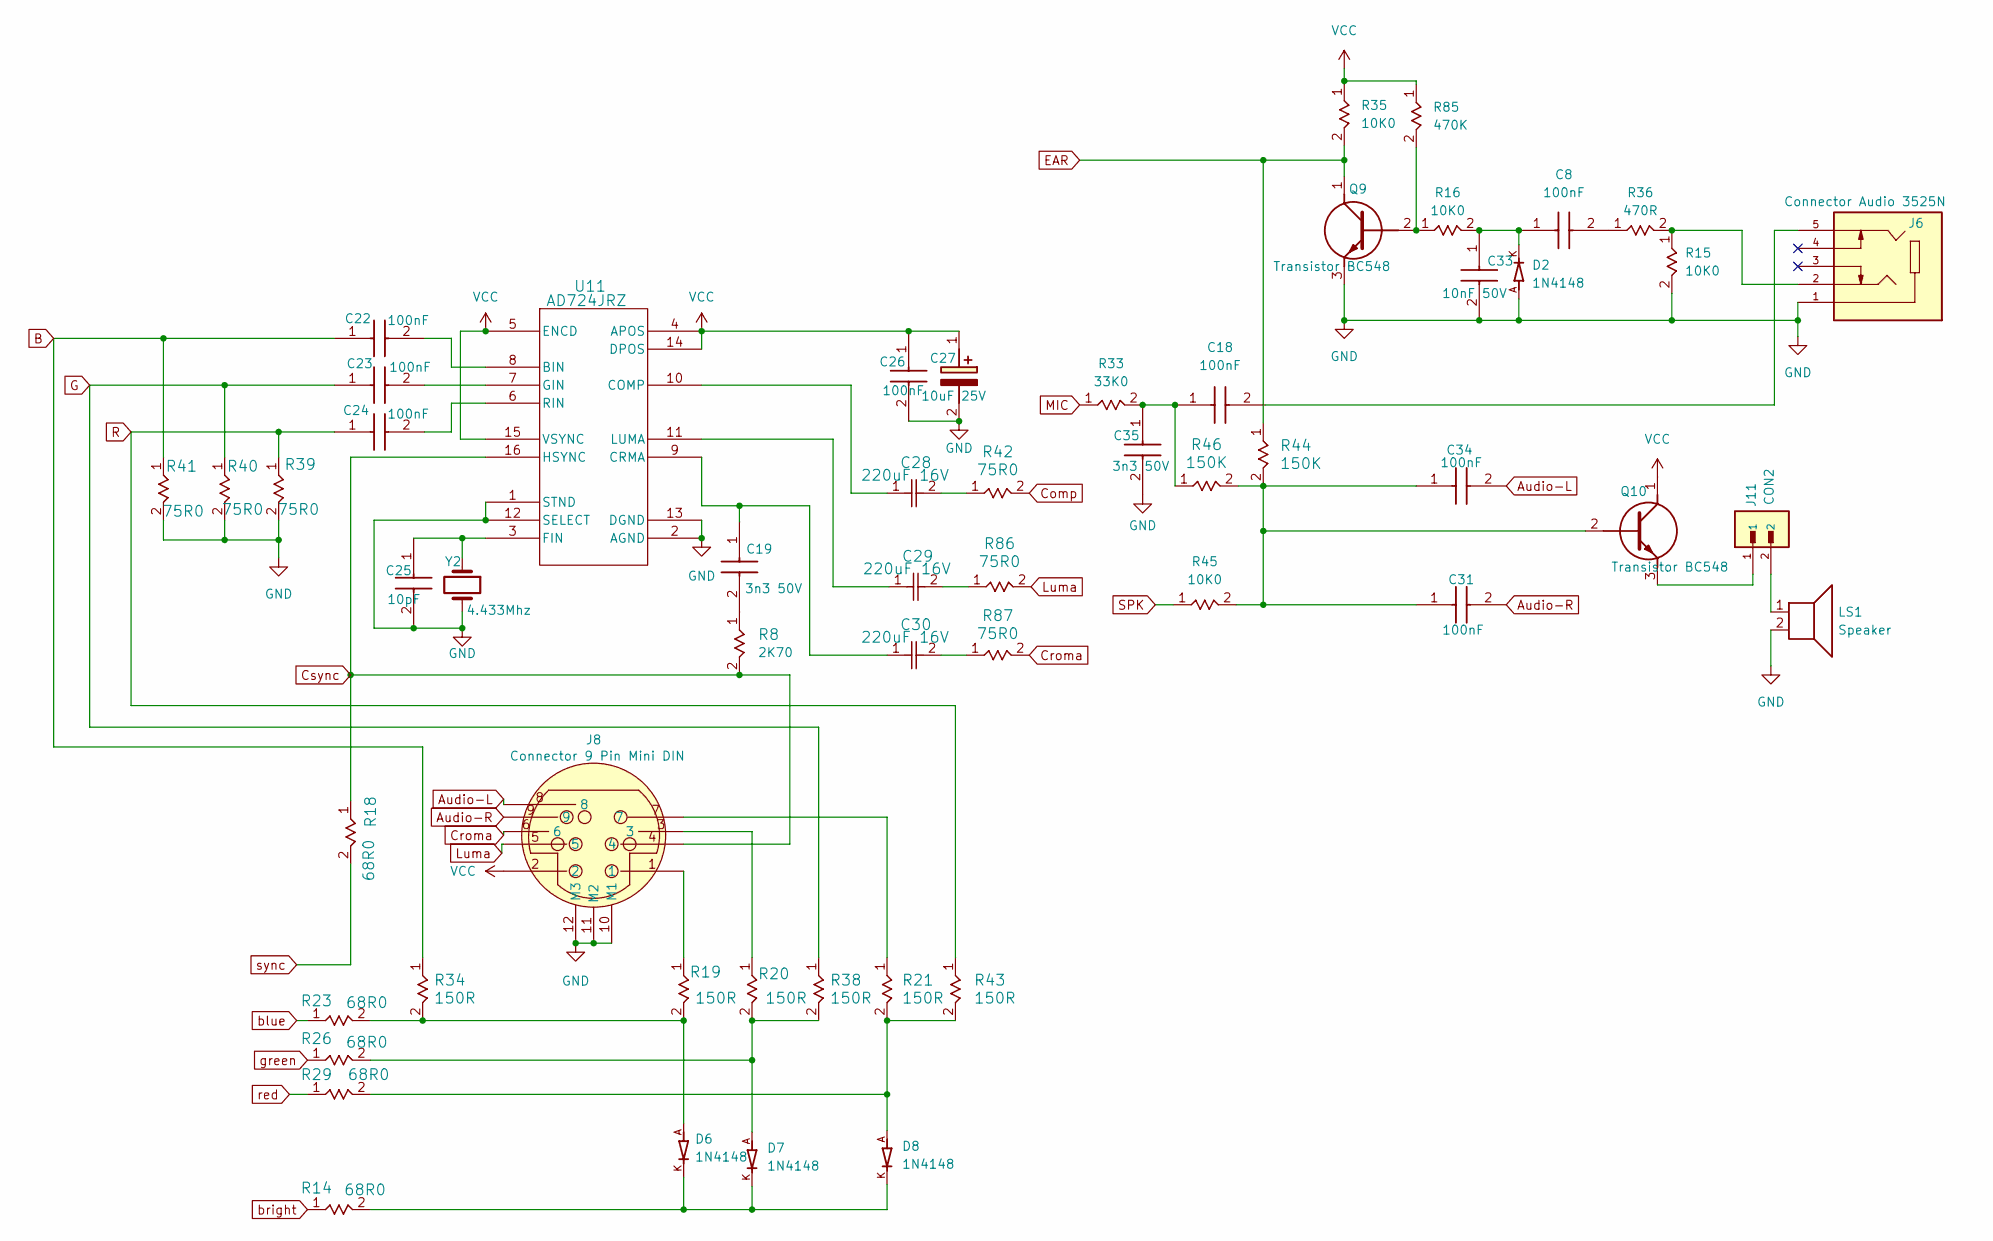
[picture p53: schematic Video.kicad_sch]

Parts:
C8, C18, C22, C23, C24, C26, C31, C34: 100nF; CAPRB250W50L400T250H550; Mouser Part Number 594-K104Z15Y5VF5TL2
C19, C35: 3n3 50V; CAPRB250W50L400T250H550; Mouser Part Number 594-K104Z15Y5VF5TL2
C25: 10pF; CAPRB250W50L400T250H550; Mouser Part Number 594-K104Z15Y5VF5TL2
C27: 10uF 25V; CAPPRD200W50D500H1100; Mouser Part Number 667-ECA-1EM100B
C28, C29, C30: 220uF 16V; CAP_YX_6P3X11_RUB
C33: 10nF 50V; CAPRB250W50L400T250H550; Mouser Part Number 594-K104Z15Y5VF5TL2
D2, D6, D7, D8: 1N4148; DIOAD753W49L380D172B; PARTREV 5
J6: Connector Audio 3525N; CUI_SJ1-3525N
J8: Connector 9 Pin Mini DIN; KMDGX9SBS1
J11: CON2; HARWIN_M20-9990246; PARTREV 14
LS1: Speaker
Q9, Q10: Transistor BC548; BC548BTA
R8: 2K70; STA_CF14_STP
R14, R18, R23, R26, R29: 68R0; STA_CF14_STP
R15, R16, R35, R45: 10K0; STA_CF14_STP
R19, R20, R21, R34, R38, R43: 150R; STA_CF14_STP
R33: 33K0; STA_CF14_STP
R36: 470R; STA_CF14_STP
R39, R40, R41, R42, R86, R87: 75R0; STA_CF14_STP
R44, R46: 150K; STA_CF14_STP
R85: 470K; STA_CF14_STP
U11: AD724JRZ; RW_16_ADI
Y2: 4.433Mhz; Crystal_HC49-4H_Vertical

Connections:
Audio-L: C34.2 (-), J8.8
Audio-R: C31.2 (-), J8.9
B: C22.1 (+), R34.1, R41.1
Comp: R42.2
Croma: J8.6, R87.2
Csync: J8.4, R8.2, R18.1, U11.16 (HSYNC)
EAR: Q9.1 (C), R35.2, R44.1
G: C23.1 (+), R38.1, R40.1
GND: C25.2 (-), C26.2 (-), C27.2 (-), C33.2 (-), C35.2 (-), D2.A, J6.1, J8.10 (M1), J8.11 (M2), J8.12 (M3), LS1.2, Q9.3 (E), R15.2, R39.2, R40.2, R41.2, U11.1 (STND), U11.2 (AGND), U11.12 (SELECT), U11.13 (DGND), Y2.2
Luma: J8.5, R86.2
MIC: R33.1
unnamed: C8.2 (-), R36.1
unnamed: C18.1 (+), C35.1 (+), R33.2, R46.1
unnamed: C18.2 (-), J6.5
unnamed: C19.1 (+), C30.1, U11.9 (CRMA)
unnamed: C19.2 (-), R8.1
unnamed: C22.2 (-), U11.8 (BIN)
unnamed: C23.2 (-), U11.7 (GIN)
unnamed: C24.2 (-), U11.6 (RIN)
unnamed: C25.1 (+), U11.3 (FIN), Y2.1
unnamed: C28.1, U11.10 (COMP)
unnamed: C28.2, R42.1
unnamed: C29.1, U11.11 (LUMA)
unnamed: C29.2, R86.1
unnamed: C30.2, R87.1
unnamed: C31.1 (+), C34.1 (+), Q10.2 (B), R44.2, R45.2, R46.2
unnamed: C8.1 (+), C33.1 (+), D2.K, R16.2
unnamed: D6.A, R19.2, R23.2, R34.2
unnamed: D6.K, D7.K, D8.K, R14.2
unnamed: D7.A, R20.2, R26.2, R38.2
unnamed: D8.A, R21.2, R29.2, R43.2
unnamed: J6.2, R15.1, R36.2
unnamed: J8.1, R19.1
unnamed: J8.3, R20.1
unnamed: J8.7, R21.1
unnamed: J11.1, Q10.3 (E)
unnamed: J11.2, LS1.1
unnamed: Q9.2 (B), R16.1, R85.2
R: C24.1 (+), R39.1, R43.1
SPK: R45.1
VCC: C26.1 (+), C27.1 (+), J8.2, Q10.1 (C), R35.1, R85.1, U11.4 (APOS), U11.5 (ENCD), U11.14 (DPOS), U11.15 (VSYNC)
blue: R23.1
bright: R14.1
green: R26.1
red: R29.1
sync: R18.2
