liveboxandy/ZX-Max-128-Issue-3A/ZX Max 128 Issue 3A PCB.kicad_sch

## KiCad design ZX Max 128 Issue 3A PCB.kicad_sch (2026-07-10)

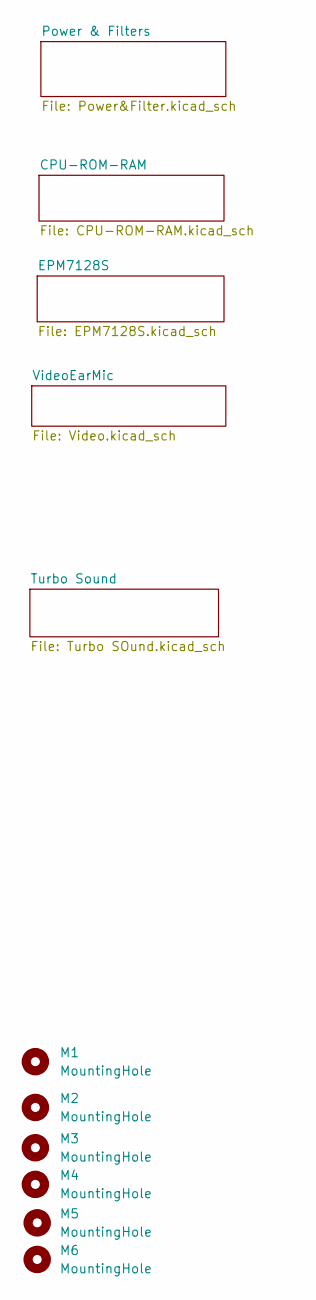
[picture p54: schematic ZX Max 128 Issue 3A PCB.kicad_sch]

Parts:
M1, M2, M3, M4, M5, M6: MountingHole; MountingHole_3.2mm_M3_DIN965
